arjepsen/Pedalboard-integrated-audio/3d-models/DF40C-100DS.stp

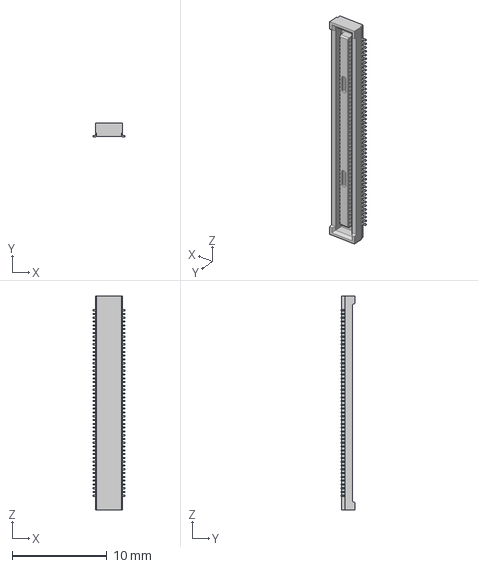
[picture p22: CAD file, 2026-09-02]
3d-models/DF40C-100DS.stp
3.38 x 1.45 x 22.6 mm
