arjepsen/Pedalboard-integrated-audio/3d-models/CM4-NANO-A.step

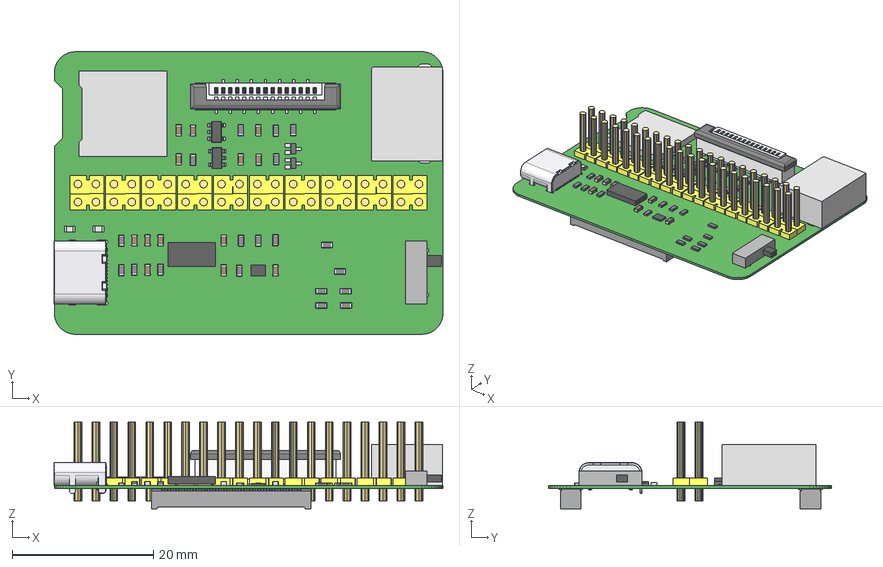
[picture p23: CAD file, 2026-09-02]
3d-models/CM4-NANO-A.step
55.1 x 40.0 x 12.3 mm
Board
RESC1608(0603) x 19
Extruded x 80
df40hc_3_0_-100ds-0_4v_58_ x 2
CAPC1608(0603) x 13
User_Library-USB-TYPE-C20
SW3DPS-SOT-23-5-DEFAULT x 2
ffc_fpc_affc10-15-100-svs-t
