arjepsen/Pedalboard-integrated-audio/3d-models/EC11E-05SW.STEP

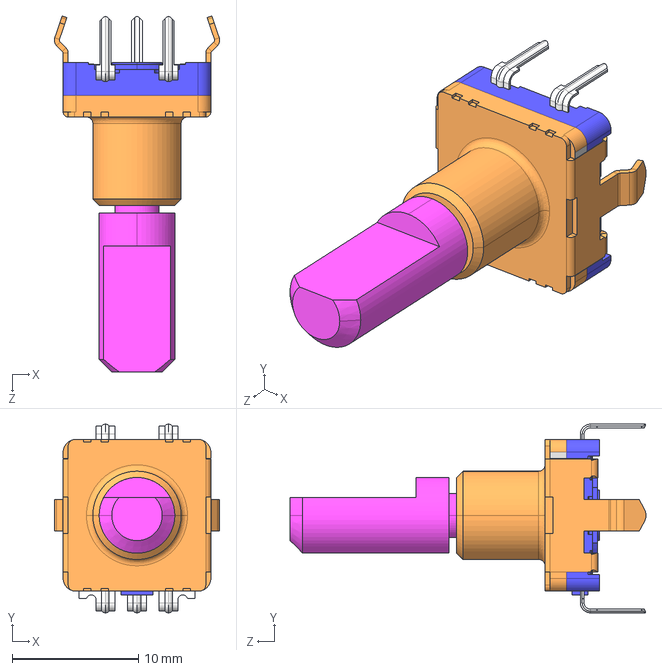
[picture p24: CAD file, 2026-09-02]
3d-models/EC11E-05SW.STEP
13.1 x 15.0 x 28.2 mm
