arjepsen/Pedalboard-integrated-audio/3d-models/B4B-PH-SM4-TB (LF)(SN).STEP

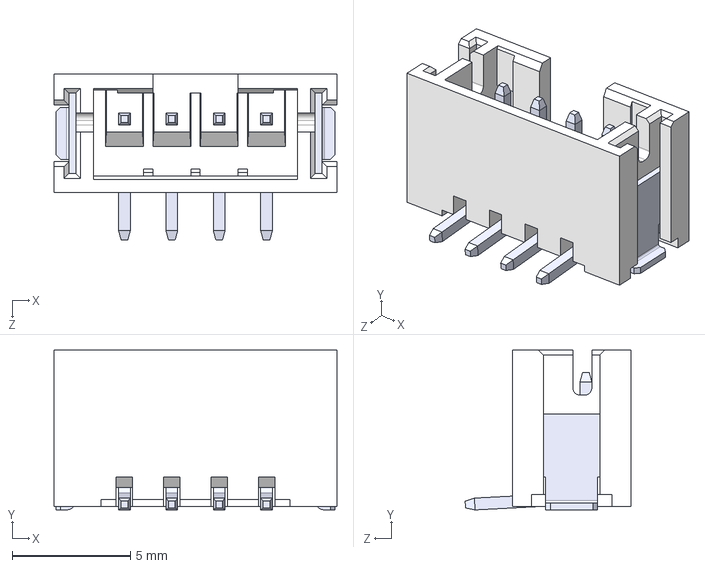
[picture p25: CAD file, 2026-09-02]
3d-models/B4B-PH-SM4-TB (LF)(SN).STEP
12.0 x 6.75 x 7.00 mm
