arjepsen/Pedalboard-integrated-audio/3d-models/mill-max-0906-2-15-20-75-14-11-0.step

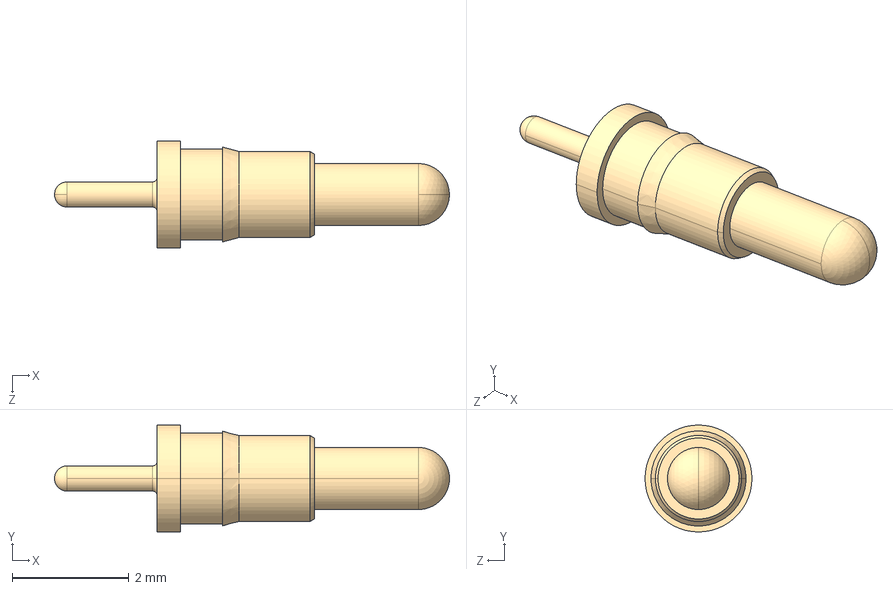
[picture p26: CAD file, 2026-09-02]
3d-models/mill-max-0906-2-15-20-75-14-11-0.step
6.76 x 1.83 x 1.83 mm
