arjepsen/Pedalboard-integrated-audio/3d-models/pedalboard-soundcard-3D.step

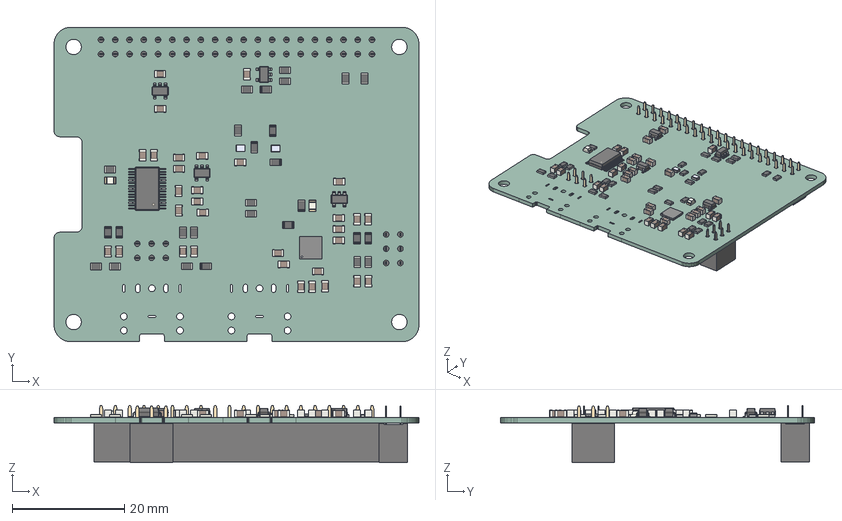
[picture p27: CAD file, 2026-09-02]
3d-models/pedalboard-soundcard-3D.step
65.0 x 56.0 x 10.2 mm
tmppicyssia PCB
