arjepsen/Pedalboard-integrated-audio/3d-models/USB1061-GF-L-A.stp

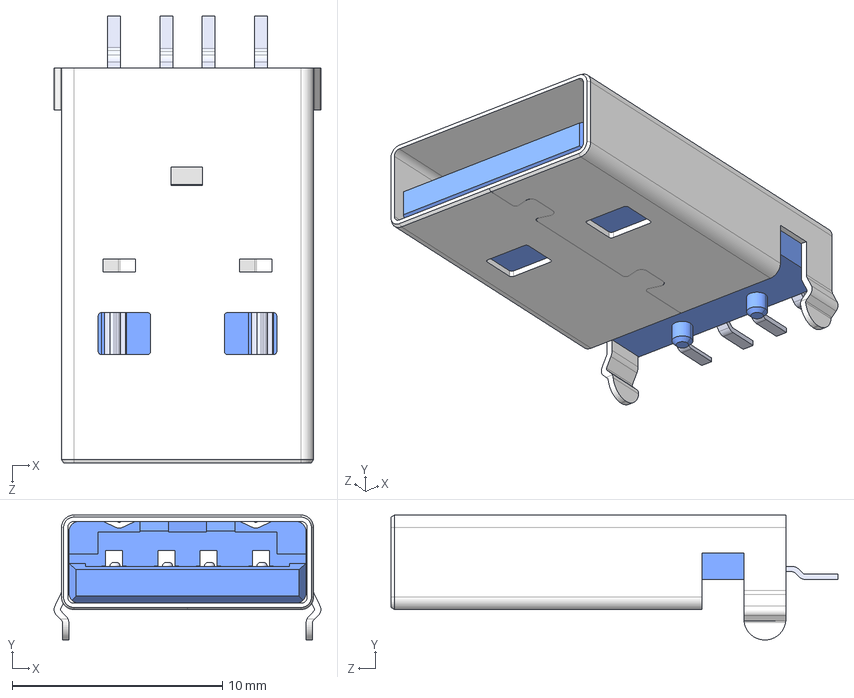
[picture p28: CAD file, 2026-09-02]
3d-models/USB1061-GF-L-A.stp
12.7 x 5.95 x 21.3 mm
USB1061-GF-L-A_PART5
USB1061-GF-L-A_PART4
USB1061-GF-L-A_PART3
USB1061-GF-L-A_PART2
USB1061-GF-L-A_PART1
