arjepsen/Pedalboard-integrated-audio/3d-models/pedalboard-led-ring-3D.step

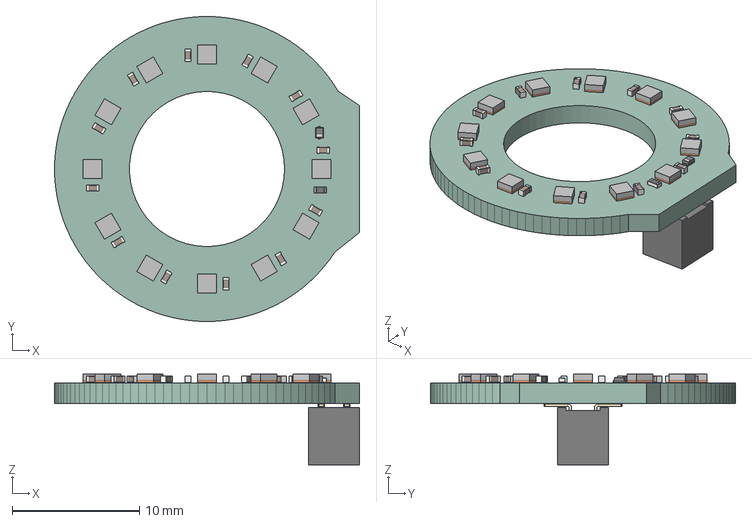
[picture p29: CAD file, 2026-09-02]
3d-models/pedalboard-led-ring-3D.step
24.0 x 24.0 x 7.15 mm
_autosave-pedalboard-led-ring PCB
