arjepsen/Pedalboard-integrated-audio/3d-models/WE-tact-button.stp

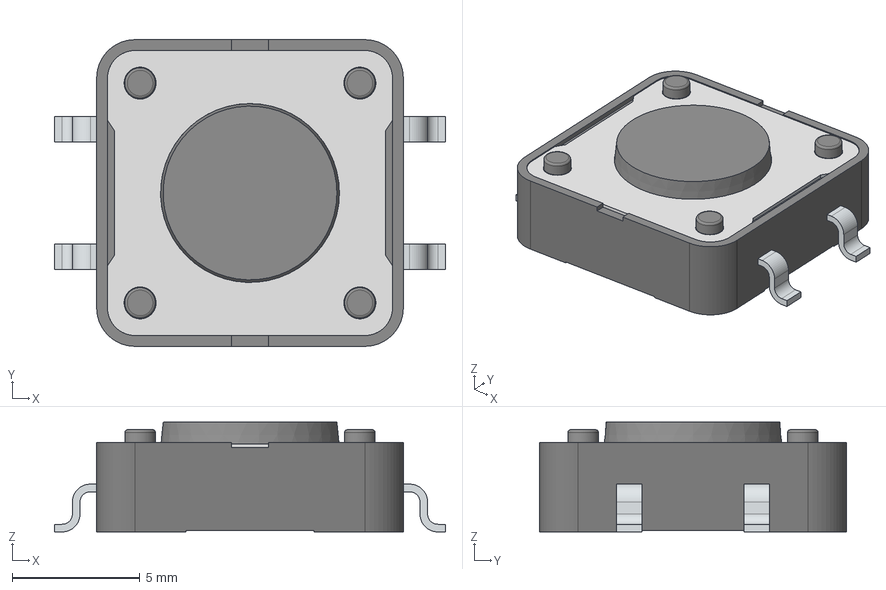
[picture p30: CAD file, 2026-09-02]
3d-models/WE-tact-button.stp
15.3 x 12.0 x 4.30 mm
Contactplates
Stem
Cover
Contact Plate
Frame
Terminal
