arjepsen/Pedalboard-integrated-audio/3d-models/USB_Micro-B_Wuerth_614105150721.step

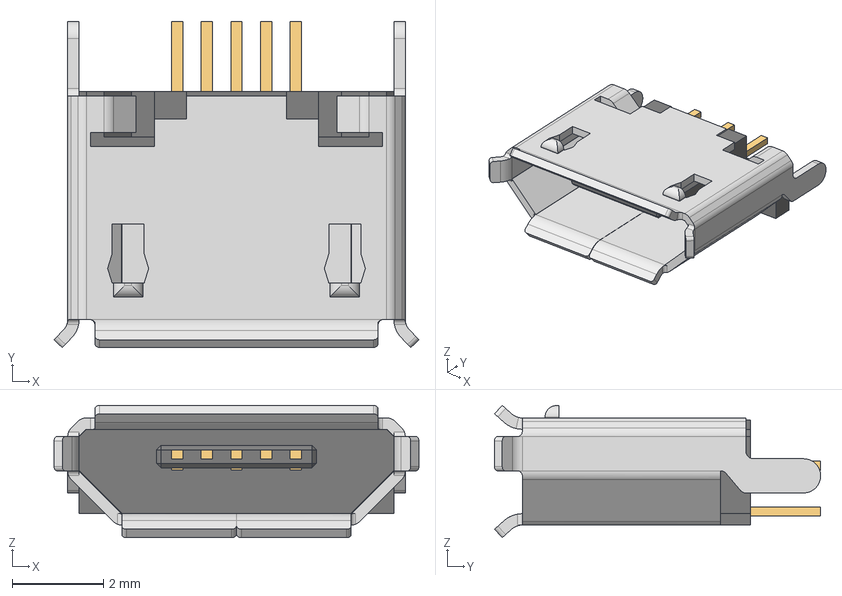
[picture p31: CAD file, 2026-09-02]
3d-models/USB_Micro-B_Wuerth_614105150721.step
8.00 x 7.15 x 2.90 mm
614105150721_Housing
614105150721_Pin1 x 3
614105150721_Pin2 x 2
614105150721_Shielding
