arjepsen/Pedalboard-integrated-audio/img/debug-audio.png

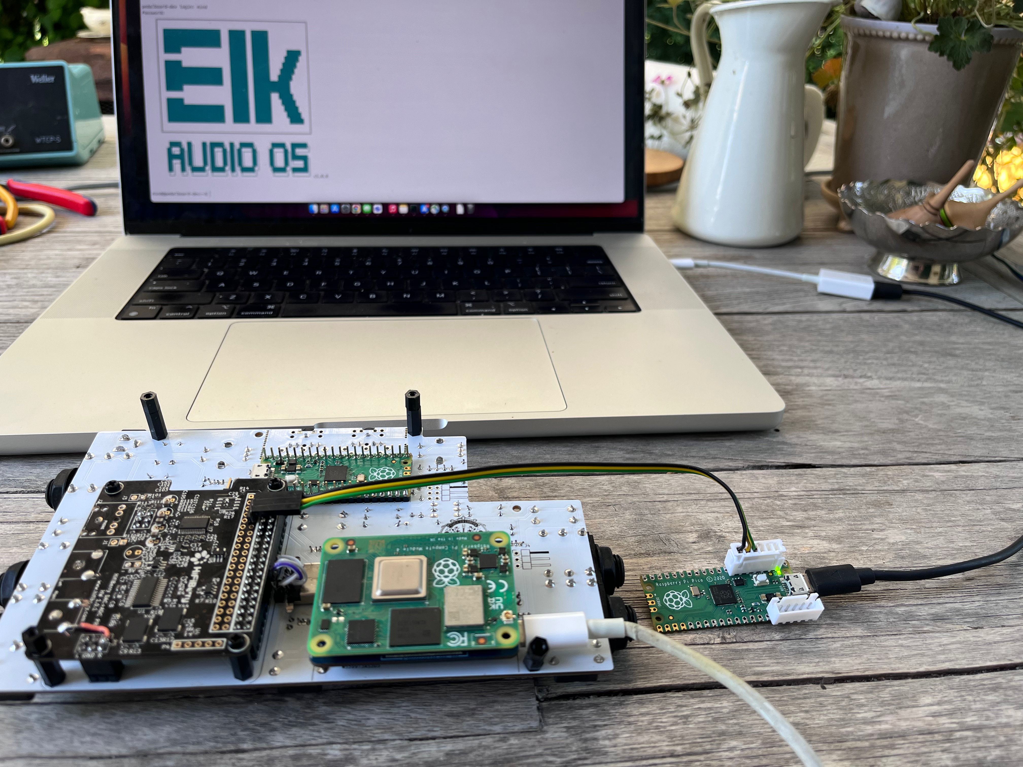
img/debug-audio.png
