arjepsen/Pedalboard-integrated-audio/img/debug-midi.png

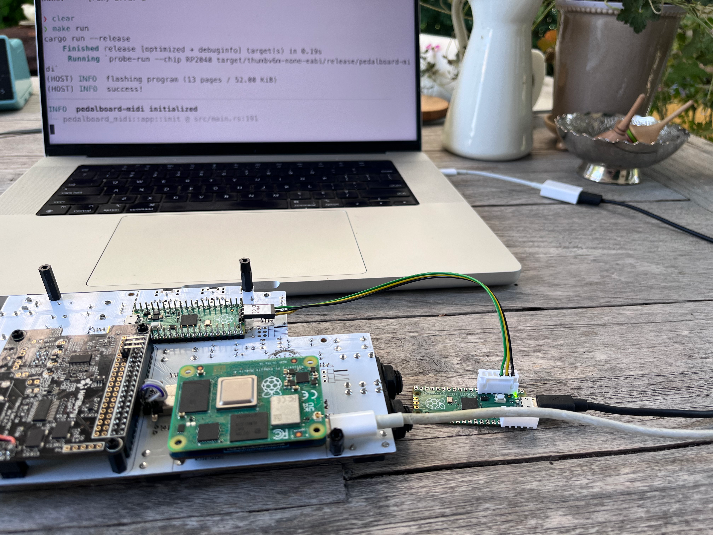
img/debug-midi.png
